arber333/Johannes-controler-Volt-Ampera-DUAL-IGBT-board/SN74L.jpg

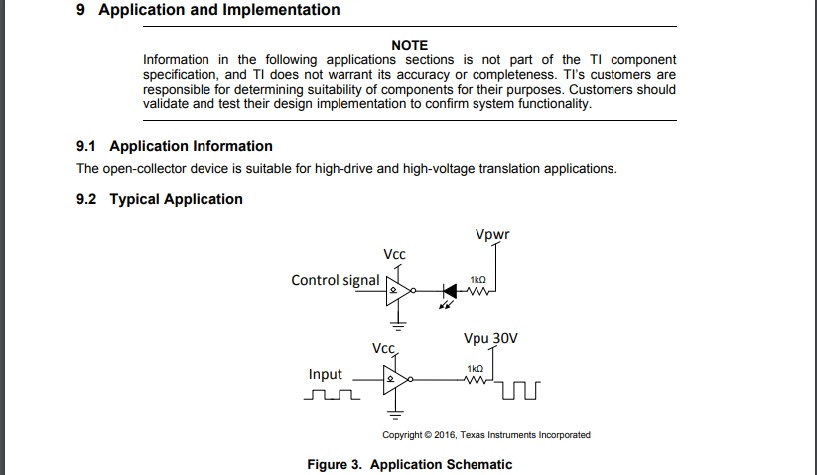
SN74L.jpg
